marekw1986/EtherGeiger/code/CustomHTTPApp.c

/*********************************************************************
 *
 *  Application to Demo HTTP2 Server
 *  Support for HTTP2 module in Microchip TCP/IP Stack
 *	 -Implements the application 
 *	 -Reference: RFC 1002
 *
 *********************************************************************
 * FileName:        CustomHTTPApp.c
 * Dependencies:    TCP/IP stack
 * Processor:       PIC18, PIC24F, PIC24H, dsPIC30F, dsPIC33F, PIC32
 * Compiler:        Microchip C32 v1.05 or higher
 *					Microchip C30 v3.12 or higher
 *					Microchip C18 v3.30 or higher
 *					HI-TECH PICC-18 PRO 9.63PL2 or higher
 * Company:         Microchip Technology, Inc.
 *
 * Software License Agreement
 *
 * Copyright (C) 2002-2010 Microchip Technology Inc.  All rights
 * reserved.
 *
 * Microchip licenses to you the right to use, modify, copy, and
 * distribute:
 * (i)  the Software when embedded on a Microchip microcontroller or
 *      digital signal controller product ("Device") which is
 *      integrated into Licensee's product; or
 * (ii) ONLY the Software driver source files ENC28J60.c, ENC28J60.h,
 *		ENCX24J600.c and ENCX24J600.h ported to a non-Microchip device
 *		used in conjunction with a Microchip ethernet controller for
 *		the sole purpose of interfacing with the ethernet controller.
 *
 * You should refer to the license agreement accompanying this
 * Software for additional information regarding your rights and
 * obligations.
 *
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
 *
 * Author               Date    Comment
 *~~~~~~~~~~~~~~~~~~~~~~~~~~~~~~~~~~~~~~~~~~~~~~~~~~~~~~~~~~~~~~~~~~~~
 * Elliott Wood     	6/18/07	Original
 ********************************************************************/
#define __CUSTOMHTTPAPP_C

#include <time.h>
#include <string.h>
#include <stdio.h>

#include "TCPIPConfig.h"
#include "config/config.h"
#include "nvram/nvram.h"
#include "time/time.h"
#include "common.h"

#if defined(STACK_USE_HTTP2_SERVER)

#include "net/TCPIP.h"

extern HTTP_CONN curHTTP;
extern HTTP_STUB httpStubs[MAX_HTTP_CONNECTIONS];
extern BYTE curHTTPID;

BYTE token[9];

#if defined (HTTP_USE_POST)
static HTTP_IO_RESULT HTTPPostConfig (void);
static HTTP_IO_RESULT HTTPPostPass (void);
#endif

enum {PASSCHANGE_UNKNOWN, PASSCHANGE_INVALID_TOKEN, PASSCHANGE_EMPTY_OLD, PASSCHANGE_WRONG_OLD, PASSCHANGE_INVALID_NEW, PASSCHANGE_OK};
enum {CFGCHANGE_UNKNOWN, CFGCHANGE_INVALID_TOKEN, CFGCHANGE_INVALID_DHCP, CFGCHANGE_INVALID_IP, CFGCHANGE_INVALID_MAC, CFGCHANGE_INVALID_NETMASK, 
      CFGCHANGE_INVALID_GW, CFGCHANGE_INVALID_DNS1, CFGCHANGE_INVALID_DNS2, CFGCHANGE_INVALID_NTP, CFGCHANGE_INVALID_TIMEZONE, CFGCHANGE_INVALID_DEVNAME, 
      CFGCHANGE_INVALID_MQTT,  CFGCHANGE_INVALID_MQTT_PORT, CFGCHANGE_INVALID_MQTT_USERNAME, CFGCHANGE_INVALID_MQTT_PASSWORD, CFGCHANGE_INVALID_TOPIC, CFGCHANGE_OK};
enum {RESTORE_UNKNOWN, RESTORE_INVALID_TOKEN, RESTORE_OK};

/*****************************************************************************
  Function:
	BYTE HTTPNeedsAuth(BYTE* cFile)
	
  Internal:
  	See documentation in the TCP/IP Stack API or HTTP2.h for details.
  ***************************************************************************/
#if defined(HTTP_USE_AUTHENTICATION)
BYTE HTTPNeedsAuth(BYTE* cFile)
{
    if(memcmppgm2ram(cFile, (ROM void*)"ui/", 3) == 0) return 0x00;
	return 0x80;
}
#endif

/*****************************************************************************
  Function:
	BYTE HTTPCheckAuth(BYTE* cUser, BYTE* cPass)
	
  Internal:
  	See documentation in the TCP/IP Stack API or HTTP2.h for details.
  ***************************************************************************/
#if defined(HTTP_USE_AUTHENTICATION)
BYTE HTTPCheckAuth(BYTE* cUser, BYTE* cPass)
{
    if(strcmppgm2ram((char *)cUser,(ROM char *)"admin") == 0
    && strcmp((char *)cPass, config.password) == 0)
    return 0x80;
	
	return 0x00;
}
#endif

/*********************************************************************
 * Function:        HTTP_IO_RESULT HTTPExecuteGet(void)
 *
 * PreCondition:    curHTTP is loaded
 *
 * Input:           None
 *
 * Output:          HTTP_IO_DONE on success
 *					HTTP_IO_WAITING if waiting for asynchronous process
 *
 * Side Effects:    None
 *
 * Overview:        This function is called if data was read from the
 *					HTTP request from either the GET arguments, or
 *					any cookies sent.  curHTTP.data contains
 *					sequential pairs of strings representing the
 *					data received.  Any required authentication has 
 *					already been validated.
 *
 * Note:            Custom implementation for WebVend Application
 ********************************************************************/
HTTP_IO_RESULT HTTPExecuteGet(void)
{
	BYTE name[20];
    BYTE* ptr;
    
    MPFSGetFilename(curHTTP.file, name, 20);
    if (strcmppgm2ram((char*)name, (ROM char*)"ui/restore.cgi") == 0) {
        ptr = HTTPGetROMArg(curHTTP.data, (ROM BYTE *)"token");
        if ( !ptr || (strcmp((char*)ptr, (char*)token) != 0) ) {
            curHTTP.data[0] = RESTORE_INVALID_TOKEN;
            return HTTP_IO_DONE;
        }
        curHTTP.data[0] = RESTORE_OK;
    }
    else if (strcmppgm2ram((char*)name, (ROM char*)"ui/getarch.cgi") == 0) {
        ptr = HTTPGetROMArg(curHTTP.data, (ROM BYTE *)"mem");
        if (!ptr) { return HTTP_IO_DONE; }
        else if ( strcmppgm2ram((char*)ptr, (ROM char*)"spi") == 0 ) {
            
        }
        else if ( strcmppgm2ram((char*)ptr, (ROM char*)"usb") == 0 ) {
            
        }
        
        ptr = HTTPGetROMArg(curHTTP.data, (ROM BYTE *)"fname");
        
    }
	return HTTP_IO_DONE;
}

#if defined(HTTP_USE_POST)

/*********************************************************************
 * Function:        HTTP_IO_RESULT HTTPExecutePost(void)
 *
 * PreCondition:    curHTTP is loaded
 *
 * Input:           None
 *
 * Output:          HTTP_IO_DONE on success
 *					HTTP_IO_NEED_DATA if more data is requested
 *					HTTP_IO_WAITING if waiting for asynchronous process
 *
 * Side Effects:    None
 *
 * Overview:        This function is called if the request method was
 *					POST.  It is called after HTTPExecuteGet and 
 *					after any required authentication has been validated.
 *
 * Note:            Custom implementation for WebVend Application
 ********************************************************************/
HTTP_IO_RESULT HTTPExecutePost(void) {
	BYTE name[20];
    
    // Load the file name
    MPFSGetFilename(curHTTP.file, name, sizeof(name));
    // Make sure it's the ui/net.htm page
    if (strcmppgm2ram((char*)name, (ROM char*)"ui/config.cgi") == 0) {
		return HTTPPostConfig();
    }
    else if (strcmppgm2ram((char*)name, (ROM char*)"ui/pass.cgi") == 0) {
        return HTTPPostPass();
    }
	return HTTP_IO_DONE;
}

static HTTP_IO_RESULT HTTPPostConfig (void) {
    WORD len;
    config_t newConfig;
    BYTE tokenValid = 0;
    
    curHTTP.data[0] = CFGCHANGE_UNKNOWN;

    // Check to see if the browser is attempting to submit more data than we can parse at once.
	if (curHTTP.byteCount > TCPIsGetReady(sktHTTP) + TCPGetRxFIFOFree(sktHTTP)) return HTTP_IO_DONE;

	// Ensure that all data is waiting to be parsed.  If not, keep waiting for all of it to arrive.
	if (TCPIsGetReady(sktHTTP) < curHTTP.byteCount) return HTTP_IO_NEED_DATA;

    eprom_read((void*)&newConfig, sizeof(newConfig));    
    	
	// Loop while data remains
	while (curHTTP.byteCount) {
		// Check for complete variable
		len = TCPFind(sktHTTP, '&', 0, FALSE);
		if ( (len == 0xFFFF) && (TCPIsGetReady(sktHTTP) == curHTTP.byteCount) ) len = curHTTP.byteCount - 1; //Check if this is the last one

		len = TCPGetArray(sktHTTP, curHTTP.data, len+1);
		curHTTP.byteCount -= len;
		curHTTP.data[len] = '\0';
		HTTPURLDecode(curHTTP.data);
		// Figure out which variable it is
		if (memcmppgm2ram(curHTTP.data, (ROM void*)"token", 5) == 0) {
             if (strcmp(&curHTTP.data[6], token) == 0 ) {
                tokenValid = 1;
            }
            else {
                curHTTP.data[0] = CFGCHANGE_INVALID_TOKEN;
                return HTTP_IO_DONE;
            }
        }
        else if (memcmppgm2ram(curHTTP.data, (ROM void*)"dhcp", 4) == 0) {
			if (memcmppgm2ram(&curHTTP.data[5], (ROM void*)"yes", 3) == 0) {
				newConfig.AppConfig.Flags.bIsDHCPEnabled = TRUE;
			}
			else if (memcmppgm2ram(&curHTTP.data[5], (ROM void*)"no", 2) == 0) {
				newConfig.AppConfig.Flags.bIsDHCPEnabled = FALSE;
			}
            else {
                curHTTP.data[0] = CFGCHANGE_INVALID_DHCP;
                return HTTP_IO_DONE;
            }
		}            
		else if (memcmppgm2ram(curHTTP.data, (ROM void*)"ip", 2) == 0) {
			if (StringToIPAddress(&curHTTP.data[3], &newConfig.AppConfig.MyIPAddr)) {
                newConfig.AppConfig.DefaultIPAddr.Val = newConfig.AppConfig.MyIPAddr.Val;
            }
            else {
                curHTTP.data[0] = CFGCHANGE_INVALID_IP;
                return HTTP_IO_DONE;
            }
		}
        else if (memcmppgm2ram(curHTTP.data, (ROM void*)"mac", 3) == 0) {
            if (StringToMACAddress(&curHTTP.data[4], &newConfig.AppConfig.MyMACAddr)) {
                
            }
            else {
                curHTTP.data[0] = CFGCHANGE_INVALID_MAC;
                return HTTP_IO_DONE;
            }
        }        
		else if (memcmppgm2ram(curHTTP.data, (ROM void*)"netmask", 7) == 0) {
			if (StringToIPAddress(&curHTTP.data[8], &newConfig.AppConfig.MyMask)) {
                newConfig.AppConfig.DefaultMask.Val = newConfig.AppConfig.MyMask.Val;
            }
            else {
                curHTTP.data[0] = CFGCHANGE_INVALID_NETMASK;
                return HTTP_IO_DONE;
            }
		}
		else if (memcmppgm2ram(curHTTP.data, (ROM void*)"gw", 2) == 0) {
			if (!StringToIPAddress(&curHTTP.data[3], &newConfig.AppConfig.MyGateway)) {
                curHTTP.data[0] = CFGCHANGE_INVALID_GW;
                return HTTP_IO_DONE;
            }
		}
		else if (memcmppgm2ram(curHTTP.data, (ROM void*)"dns1", 4) == 0) {
			if (!StringToIPAddress(&curHTTP.data[5], &newConfig.AppConfig.PrimaryDNSServer)) {
                curHTTP.data[0] = CFGCHANGE_INVALID_DNS1;
                return HTTP_IO_DONE;
            }
		}
		else if (memcmppgm2ram(curHTTP.data, (ROM void*)"dns2", 4) == 0) {
			if (!StringToIPAddress(&curHTTP.data[5], &newConfig.AppConfig.SecondaryDNSServer)) {
                curHTTP.data[0] = CFGCHANGE_INVALID_DNS2;
                return HTTP_IO_DONE;
            }
		}
		else if (memcmppgm2ram(curHTTP.data, (ROM void*)"ntp", 3) == 0) {
            if (strlen(&curHTTP.data[4]) && !contain_space(&curHTTP.data[4])) {
                strncpy(newConfig.AppConfig.NtpServer, &curHTTP.data[4], sizeof(newConfig.AppConfig.NtpServer));
            }
            else {
                curHTTP.data[0] = CFGCHANGE_INVALID_NTP;
                return HTTP_IO_DONE;
            }
		}
		else if (memcmppgm2ram(curHTTP.data, (ROM void*)"timezone", 8) == 0) {
            newConfig.timeZone = atoi(&curHTTP.data[9]) * -60;
            if ( (newConfig.timeZone < -780) || (newConfig.timeZone > 660) ) {
                curHTTP.data[0] = CFGCHANGE_INVALID_TIMEZONE;
                return HTTP_IO_DONE;
            }
		}
        else if (memcmppgm2ram(curHTTP.data, (ROM void*)"mqttserver", 10) == 0) {
            if ( (strlen(&curHTTP.data[11]) < sizeof(newConfig.mqtt_server)) && !contain_space(&curHTTP.data[11]) ) {strncpy(newConfig.mqtt_server, &curHTTP.data[11], sizeof(newConfig.mqtt_server)-1);}
            else {
                curHTTP.data[0] = CFGCHANGE_INVALID_MQTT;
                return HTTP_IO_DONE;
            }
        }
        else if (memcmppgm2ram(curHTTP.data, (ROM void*)"mqttusername", 12) == 0) {
            if ( (strlen(&curHTTP.data[13]) < sizeof(newConfig.mqtt_username)) && !contain_space(&curHTTP.data[13]) ) {strncpy(newConfig.mqtt_username, &curHTTP.data[13], sizeof(newConfig.mqtt_username)-1);}
            else {
                curHTTP.data[0] = CFGCHANGE_INVALID_MQTT_USERNAME;
                return HTTP_IO_DONE;
            }
        }
        else if (memcmppgm2ram(curHTTP.data, (ROM void*)"mqttpassword", 12) == 0) {
            if ( (strlen(&curHTTP.data[13]) < sizeof(newConfig.mqtt_password)) && !contain_space(&curHTTP.data[13]) ) {strncpy(newConfig.mqtt_password, &curHTTP.data[13], sizeof(newConfig.mqtt_password)-1);}
            else {
                curHTTP.data[0] = CFGCHANGE_INVALID_MQTT_PASSWORD;
                return HTTP_IO_DONE;
            }
        }         
        else if (memcmppgm2ram(curHTTP.data, (ROM void*)"mqttport", 8) == 0) {
            uint32_t tmpval = strtol(&curHTTP.data[9], NULL, 10);
            if (tmpval) {
                newConfig.mqtt_port = tmpval;
            }
            else {
                curHTTP.data[0] = CFGCHANGE_INVALID_MQTT_PORT;
                return HTTP_IO_DONE;                
            }
        }
        else if (memcmppgm2ram(curHTTP.data, (ROM void*)"topic", 5) == 0) {
            if ( (strlen(&curHTTP.data[6]) < sizeof(newConfig.mqtt_topic)) && !contain_space(&curHTTP.data[6]) ) {strncpy(newConfig.mqtt_topic, &curHTTP.data[6], sizeof(newConfig.mqtt_topic)-1);}
            else {
                curHTTP.data[0] = CFGCHANGE_INVALID_TOPIC;
                return HTTP_IO_DONE;                   
            }
        }
        else if (memcmppgm2ram(curHTTP.data, (ROM void*)"devname", 7) == 0) {
            if ( (strlen(&curHTTP.data[8]) < sizeof(newConfig.devname)) && !contain_space(&curHTTP.data[8])) {
                strncpy(newConfig.devname, &curHTTP.data[8], sizeof(newConfig.devname)-1);
            }
            else {
                curHTTP.data[0] = CFGCHANGE_INVALID_DEVNAME;
                return HTTP_IO_DONE;                      
            }
        }
	}   
    
    if (!tokenValid) {
        curHTTP.data[0] = CFGCHANGE_INVALID_TOKEN;
        return HTTP_IO_DONE;
    }
    
	// Tu zapisujemy zmiany
    eprom_write((void*)&newConfig, sizeof(newConfig));
    curHTTP.data[0] = CFGCHANGE_OK;
	return HTTP_IO_DONE;
}

static HTTP_IO_RESULT HTTPPostPass (void) {
    WORD len;
    config_t newConfig;
    BYTE tokenValid = 0;
    BYTE passValid = 0;
    
    curHTTP.data[0] = PASSCHANGE_UNKNOWN;
    
     // Check to see if the browser is attempting to submit more data than we can parse at once.
	if (curHTTP.byteCount > TCPIsGetReady(sktHTTP) + TCPGetRxFIFOFree(sktHTTP)) return HTTP_IO_DONE;

	// Ensure that all data is waiting to be parsed.  If not, keep waiting for all of it to arrive.
	if (TCPIsGetReady(sktHTTP) < curHTTP.byteCount) return HTTP_IO_NEED_DATA;
    
    eprom_read((void*)&newConfig, sizeof(newConfig));
    
	// Loop while data remains
	while (curHTTP.byteCount) {
		// Check for complete variable
		len = TCPFind(sktHTTP, '&', 0, FALSE);
        if ( (len == 0xFFFF) && (TCPIsGetReady(sktHTTP) == curHTTP.byteCount) ) len = curHTTP.byteCount - 1; //Check if this is the last one

		len = TCPGetArray(sktHTTP, curHTTP.data, len+1);
		curHTTP.byteCount -= len;
		curHTTP.data[len] = '\0';
		HTTPURLDecode(curHTTP.data);
		// Figure out which variable it is
		if (memcmppgm2ram(curHTTP.data, (ROM void*)"token", 5) == 0) {
            if (strcmp(&curHTTP.data[6], token) == 0 ) {
                tokenValid = 1;
            }
            else {
                curHTTP.data[0] = PASSCHANGE_INVALID_TOKEN;                
                return HTTP_IO_DONE;                
            }
		}          
		else if (memcmppgm2ram(curHTTP.data, (ROM void*)"oldpass", 7) == 0) {
			if (strlen(&curHTTP.data[8]) == 0) {
                curHTTP.data[0] = PASSCHANGE_EMPTY_OLD;                
                return HTTP_IO_DONE;
            }
            if (strcmp(&curHTTP.data[8], config.password) == 0 ) {
                passValid = 1;
            }
            else {
                curHTTP.data[0] = PASSCHANGE_WRONG_OLD;                
                return HTTP_IO_DONE;                
            }
		}            
		else if (memcmppgm2ram(curHTTP.data, (ROM void*)"newpass", 7) == 0) {
			if (strlen(&curHTTP.data[8]) == 0) {
                curHTTP.data[0] = PASSCHANGE_INVALID_NEW; 
                return HTTP_IO_DONE;
            }
            strncpy(newConfig.password, &curHTTP.data[8], sizeof(newConfig.password));
		}        
	}
    
    if (!tokenValid || !passValid) return HTTP_IO_DONE;
    
	// Saving new configuration to flash
    eprom_write((void*)&newConfig, sizeof(newConfig));
    curHTTP.data[0] = PASSCHANGE_OK; 
	return HTTP_IO_DONE;
}

#endif //(use_post)

/*********************************************************************
 * Function:        void HTTPPrint_varname(TCP_SOCKET sktHTTP, 
 *							DWORD callbackPos, BYTE *data)
 *
 * PreCondition:    None
 *
 * Input:           sktHTTP: the TCP socket to which to write
 *					callbackPos: 0 initially
 *						return value of last call for subsequent callbacks
 *					data: this connection's data buffer
 *
 * Output:          0 if output is complete
 *					application-defined otherwise
 *
 * Side Effects:    None
 *
 * Overview:        Outputs a variable to the HTTP client.
 *
 * Note:            Return zero to indicate that this callback function 
 *					has finished writing data to the TCP socket.  A 
 *					non-zero return value indicates that more data 
 *					remains to be written, and this callback should 
 *					be called again when more space is available in 
 *					the TCP TX FIFO.  This non-zero return value will 
 *					be the value of the parameter callbackPos for the 
 *					next call.
 ********************************************************************/


void HTTPPrint_dhcpyes(void) {
    if (DHCPIsEnabled(0)) {
        TCPPutROMString(sktHTTP, (ROM void*)" checked");
    }
    return;
}

void HTTPPrint_dhcpno(void) {
    if (!DHCPIsEnabled(0)) {
        TCPPutROMString(sktHTTP, (ROM void*)" checked");
    }    
    return;
}

void HTTPPrint_ipdisp(void) {
    if (DHCPIsEnabled(0)) {
        TCPPutROMString(sktHTTP, (ROM void*)"none");
    }
    else {
        TCPPutROMString(sktHTTP, (ROM void*)"block");
    }
    return;
}

void HTTPPrint_ip(void) {
    int i;
    char buf[4];
    
    for (i=0; i<4; i++) {
        TCPPutString(sktHTTP, itoa(buf, AppConfig.MyIPAddr.v[i], 10));
        if (i < 3) TCPPutROMString(sktHTTP, (ROM void*)".");
    }
    return;
}

void HTTPPrint_mac(void) {
    int i;
    char buf[4];
    
    for (i=0; i<6; i++) {
        snprintf(buf, 3, "%02X", AppConfig.MyMACAddr.v[i]);
        TCPPutString(sktHTTP, buf);
        if (i<5) TCPPutROMString(sktHTTP, (ROM void*)":");
    }
}

void HTTPPrint_netmask(void) {
    int i;
    char buf[4];
    
    for (i=0; i<4; i++) {
        TCPPutString(sktHTTP, itoa(buf, AppConfig.MyMask.v[i], 10));
        if (i < 3) TCPPutROMString(sktHTTP, (ROM void*)".");
    }    
    return;
}

void HTTPPrint_gw(void) {
    int i;
    char buf[4];
    
    for (i=0; i<4; i++) {
        TCPPutString(sktHTTP, itoa(buf, AppConfig.MyGateway.v[i], 10));
        if (i < 3) TCPPutROMString(sktHTTP, (ROM void*)".");
    }    
    return;
}

void HTTPPrint_dns1(void) {
    int i;
    char buf[4];
    
    for (i=0; i<4; i++) {
        TCPPutString(sktHTTP, itoa(buf, AppConfig.PrimaryDNSServer.v[i], 10));
        if (i < 3) TCPPutROMString(sktHTTP, (ROM void*)".");
    }    
    return;
}

void HTTPPrint_dns2(void) {
    int i;
    char buf[4];
    
    for (i=0; i<4; i++) {
        TCPPutString(sktHTTP, itoa(buf, AppConfig.SecondaryDNSServer.v[i], 10));
        if (i < 3) TCPPutROMString(sktHTTP, (ROM void*)".");
    }    
    return;
}

void HTTPPrint_ntp(void) {
    TCPPutString(sktHTTP, AppConfig.NtpServer);
    return;
}

void HTTPPrint_devname(void) {
    TCPPutString(sktHTTP, config.devname);
    return;
}

void HTTPPrint_mqtt_server(void) {
    TCPPutString(sktHTTP, config.mqtt_server);
    return;
}

void HTTPPrint_mqtt_username(void) {
    TCPPutString(sktHTTP, config.mqtt_username);
    return;
}

void HTTPPrint_mqtt_topic(void) {
    TCPPutString(sktHTTP, config.mqtt_topic);
    return;
}

void HTTPPrint_mqtt_port(void) {
    char tmp[32];
    TCPPutString(sktHTTP, itoa(tmp, config.mqtt_port, 10));
    return;
}

void HTTPPrint_newip(void) {
    config_t newConfig;
    int i;
    char buf[4];
    
    eprom_read((void*)&newConfig, sizeof(newConfig));
    
    for (i=0; i<4; i++) {
        TCPPutString(sktHTTP, itoa(buf, newConfig.AppConfig.MyIPAddr.v[i], 10));
        if (i < 3) TCPPutROMString(sktHTTP, (ROM void*)".");
    }
    return;
}

void HTTPPrint_reset(void) {
    Reset();
}

void HTTPPrint_restore(void) {
    switch(curHTTP.data[0]) {
        case RESTORE_INVALID_TOKEN:
        TCPPutROMString(sktHTTP, (ROM void*)"invalid token");
        break;
        
        case RESTORE_OK:
        loadDefaultSettings();
        eprom_write((void*)&config, sizeof(config));
        FormatSpiFlashDisk();
        TCPPutROMString(sktHTTP, (ROM void*)"ok");    
        break;
        
        default:
        TCPPutROMString(sktHTTP, (ROM void*)"unknown_error");
        break;        
    }
}

void HTTPPrint_passChangeStatus (void) {
    switch (curHTTP.data[0]) {
        case PASSCHANGE_INVALID_TOKEN:
        TCPPutROMString(sktHTTP, (ROM void*)"invalid_token");
        break;
                    
        case PASSCHANGE_EMPTY_OLD:
        TCPPutROMString(sktHTTP, (ROM void*)"empty_old");
        break;
        
        case PASSCHANGE_WRONG_OLD:
        TCPPutROMString(sktHTTP, (ROM void*)"wrong_old");  
        break;
        
        case PASSCHANGE_INVALID_NEW:
        TCPPutROMString(sktHTTP, (ROM void*)"invalid_new");
        break;
        
        case PASSCHANGE_OK:
        TCPPutROMString(sktHTTP, (ROM void*)"ok");
        break;
        
        default:
        TCPPutROMString(sktHTTP, (ROM void*)"unknown_error");
        break;
    }
}

void HTTPPrint_configChangeStatus (void) {
    switch (curHTTP.data[0]) {
        case CFGCHANGE_INVALID_TOKEN:
        TCPPutROMString(sktHTTP, (ROM void*)"invalid_token");
        break;
                    
        case CFGCHANGE_INVALID_DHCP:
        TCPPutROMString(sktHTTP, (ROM void*)"invalid_dhcp");
        break;
        
        case CFGCHANGE_INVALID_IP:
        TCPPutROMString(sktHTTP, (ROM void*)"invalid_ip");  
        break;
        
        case CFGCHANGE_INVALID_MAC:
        TCPPutROMString(sktHTTP, (ROM void*)"invalid_mac");  
        break;           
        
        case CFGCHANGE_INVALID_NETMASK:
        TCPPutROMString(sktHTTP, (ROM void*)"invalid_netmask");
        break;
        
        case CFGCHANGE_INVALID_GW:
        TCPPutROMString(sktHTTP, (ROM void*)"invalid_gw");
        break;
        
        case CFGCHANGE_INVALID_DNS1:
        TCPPutROMString(sktHTTP, (ROM void*)"invalid_dns1");
        break;
        
        case CFGCHANGE_INVALID_DNS2:
        TCPPutROMString(sktHTTP, (ROM void*)"invalid_dns2");
        break;
        
        case CFGCHANGE_INVALID_NTP:
        TCPPutROMString(sktHTTP, (ROM void*)"invalid_ntp");
        break;
        
        case CFGCHANGE_INVALID_TIMEZONE:
        TCPPutROMString(sktHTTP, (ROM void*)"invalid_timezone");
        break;
        
        case CFGCHANGE_INVALID_MQTT:
        TCPPutROMString(sktHTTP, (ROM void*)"invalid_mqtt");
        break;
        
        case CFGCHANGE_INVALID_MQTT_PORT:
        TCPPutROMString(sktHTTP, (ROM void*)"invalid_mqttport");
        break;
        
        case CFGCHANGE_INVALID_MQTT_USERNAME:
        TCPPutROMString(sktHTTP, (ROM void*)"invalid_mqttusername");
        break;

        case CFGCHANGE_INVALID_MQTT_PASSWORD:
        TCPPutROMString(sktHTTP, (ROM void*)"invalid_mqttpassword");
        break;        

        case CFGCHANGE_INVALID_TOPIC:
        TCPPutROMString(sktHTTP, (ROM void*)"invalid_topic");
        break;        
        
        case CFGCHANGE_INVALID_DEVNAME:
        TCPPutROMString(sktHTTP, (ROM void*)"invalid_devname");
        break;        
        
        case CFGCHANGE_OK:
        TCPPutROMString(sktHTTP, (ROM void*)"ok");
        break;
        
        default:
        TCPPutROMString(sktHTTP, (ROM void*)"unknown_error");
        break;
    }
}

void HTTPPrint_configToken (void) {
    BYTE i;
    for (i=0; i<8; i++) token[i] = 'a'+(rand() % 26);
    token[8] = '\0';
    TCPPutString(sktHTTP, token);
}

void HTTPPrint_uptime (void) {
    WORD days, hours, minutes;
    DWORD seconds;
    BYTE buff[32];
    
    seconds = uptime();
    
    days = seconds / 86400;
    seconds -= days * 86400;
    hours = seconds / 3600;
    seconds -= hours * 3600;
    minutes = seconds / 60;
    seconds -= minutes * 60;
 
    if (days) {
        sprintf(buff, "%d dni, ", days);
        TCPPutString(sktHTTP, buff);
    }
    sprintf(buff, "%02d:%02d:%02d", hours, minutes, seconds);
    TCPPutString(sktHTTP, buff);
}

void HTTPPrint_uptimesec (void) {
    BYTE buff[16];
    sprintf(buff, "%lu", uptime());
    TCPPutString(sktHTTP, buff);
}

void HTTPPrint_time (void) {
    BYTE buff[64];
    time_t timestamp; 
    
    timestamp = rtccGetTimestamp();
    strncpy(buff, ctime(&timestamp), sizeof(buff)-1);
    TCPPutString(sktHTTP, buff);
}

void HTTPPrint_timestamp (void) {
    BYTE buff[32];

    sprintf(buff, "%lu", rtccGetTimestamp());
    TCPPutString(sktHTTP, buff);
}

void HTTPPrint_timezone (void) {
    BYTE buff[16];
    
    sprintf(buff, "%d", time_zone/-60);
    TCPPutString(sktHTTP, buff);
    
}

void HTTPPrint_cpufreq (void) {
    BYTE buff[16];
    time_t timestamp;
    
    sprintf(buff, "%d", SYSCLK/1000000);
    TCPPutString(sktHTTP, buff);
}

void HTTPPrint_mqttupdate (void) {
    BYTE buff[64];
    if (mqtt_last_publish) {
        snprintf(buff, sizeof(buff)-1, "%d sek. temu", uptime()-mqtt_last_publish);
    }
    else {
        strncpy(buff, "nigdy", sizeof(buff)-1);
    }
    TCPPutString(sktHTTP, buff);
}

void HTTPPrint_mqttstatus (void) {
    TCPPutString(sktHTTP, MQTTConnected() ? "Polaczony" : "Rozlaczony");
}

void HTTPPrint_sensors (void) {
    BYTE buff[512];
    constructJSON((char*)buff, sizeof(buff)-1);
    TCPPutString(sktHTTP, buff);
}

void HTTPPrint_showarch (void) {
    FRESULT res;
    DIR dir;
    static FILINFO fno;
    
    uint16_t i;
    uint8_t first_disk = 1;
    char buff[64];
    
    TCPPutROMString(sktHTTP, (ROM void*)"{\n");
    
    res = f_opendir(&dir, "0:/");
    if (res == FR_OK) {
        if (!first_disk) TCPPutROMString(sktHTTP, (ROM void*)",\n");
        TCPPutROMString(sktHTTP, (ROM void*)"\"spi\" : [\n");
        for (i=0;;i++) {
            res = f_readdir(&dir, &fno);
            if (res != FR_OK || fno.fname[0] == 0) break;
            if (!(fno.fattrib & AM_DIR)) { // It is not a directory
                TCPPutROMString(sktHTTP, (ROM void*)((i > 0) ? ",\n\t{" : "\t{"));
                //json data constructed here
                TCPPutROMString(sktHTTP, (ROM void*)"\"filename\" : \"");
                TCPPutString(sktHTTP, fno.fname);
                TCPPutROMString(sktHTTP, (ROM void*)"\", \"filesize\" : ");
                snprintf(buff, sizeof(buff)-2, "%lu}\n", fno.fsize);
                TCPPutString(sktHTTP, buff);
            }    
        }
        TCPPutROMString(sktHTTP, (ROM void*)"]");
        f_closedir(&dir);
        first_disk = 0;
    }
    
    res = f_opendir(&dir, "1:/");
        if (res == FR_OK) {
        if (!first_disk) TCPPutROMString(sktHTTP, (ROM void*)",\n"); 
        TCPPutROMString(sktHTTP, (ROM void*)"\"usb\" : [\n");
        for (i=0;;i++) {
            res = f_readdir(&dir, &fno);
            if (res != FR_OK || fno.fname[0] == 0) break;
            if (!(fno.fattrib & AM_DIR)) { // It is not a directory
                TCPPutROMString(sktHTTP, (ROM void*)((i > 0) ? ",\n{\t" : "\t{"));
                //json data constructed here
                TCPPutROMString(sktHTTP, (ROM void*)"\"filename\" : \"");
                TCPPutString(sktHTTP, fno.fname);
                TCPPutROMString(sktHTTP, (ROM void*)"\", \"filesize\" : ");
                snprintf(buff, sizeof(buff)-2, "%lu}\n", fno.fsize);
                TCPPutString(sktHTTP, buff);
            }    
        }
        TCPPutROMString(sktHTTP, (ROM void*)"]\n");
        f_closedir(&dir);
        first_disk = 0;
    }
    
    TCPPutROMString(sktHTTP, (ROM void*)"\n}");
}

#endif
