marekw1986/EtherGeiger/code/net/SNTP.c

/*********************************************************************
 *
 *	Simple Network Time Protocol (SNTP) Client Version 3
 *  Module for Microchip TCP/IP Stack
 *	 -Locates an NTP Server from public site using DNS
 *	 -Requests UTC time using SNTP and updates SNTPTime structure
 *	  periodically, according to NTP_QUERY_INTERVAL value
 *	- Reference: RFC 1305
 *
 *********************************************************************
 * FileName:        SNTP.c
 * Dependencies:    UDP, ARP, DNS, Tick
 * Processor:       PIC18, PIC24F, PIC24H, dsPIC30F, dsPIC33F, PIC32
 * Compiler:        Microchip C32 v1.05 or higher
 *					Micrrtochip C30 v3.12 or higher
 *					Microchip C18 v3.30 or higher
 *					HI-TECH PICC-18 PRO 9.63PL2 or higher
 * Company:         Microchip Technology, Inc.
 *
 * Software License Agreement
 *
 * Copyright (C) 2002-2009 Microchip Technology Inc.  All rights
 * reserved.
 *
 * Microchip licenses to you the right to use, modify, copy, and
 * distribute:
 * (i)  the Software when embedded on a Microchip microcontroller or
 *      digital signal controller product ("Device") which is
 *      integrated into Licensee's product; or
 * (ii) ONLY the Software driver source files ENC28J60.c, ENC28J60.h,
 *		ENCX24J600.c and ENCX24J600.h ported to a non-Microchip device
 *		used in conjunction with a Microchip ethernet controller for
 *		the sole purpose of interfacing with the ethernet controller.
 *
 * You should refer to the license agreement accompanying this
 * Software for additional information regarding your rights and
 * obligations.
 *
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
 *
 * Author               Date    	Comment
 *~~~~~~~~~~~~~~~~~~~~~~~~~~~~~~~~~~~~~~~~~~~~~~~~~~~~~~~~~~~~~~~~~~~~
 * Darren Wenn			03/08/07	Original
 * Howard Schlunder		06/20/07	Modified for release
 ********************************************************************/
#define __SNTP_C

#include "../TCPIPConfig.h"

#if defined(STACK_USE_SNTP_CLIENT)

#include "TCPIP.h"

#ifdef SNTP_UPDATE_RTCC
#include <plib.h>
#include <time.h>
extern BYTE rtccSet;
#endif


// Defines how frequently to resynchronize the date/time (default: 10 minutes)
#define NTP_QUERY_INTERVAL		(10ull*60ull * TICK_SECOND)

// Defines how long to wait to retry an update after a failure.
// Updates may take up to 6 seconds to fail, so this 14 second delay is actually only an 8-second retry.
#define NTP_FAST_QUERY_INTERVAL	(14ull * TICK_SECOND)

// Port for contacting NTP servers
#define NTP_SERVER_PORT			(123ul)

// Reference Epoch to use.  (default: 01-Jan-1970 00:00:00)
#define NTP_EPOCH 				(86400ul * (365ul * 70ul + 17ul))

// Defines how long to wait before assuming the query has failed
#define NTP_REPLY_TIMEOUT		(6ul*TICK_SECOND)

// These are normally available network time servers.
// The actual IP returned from the pool will vary every
// minute so as to spread the load around stratum 1 timeservers.
// For best accuracy and network overhead you should locate the 
// pool server closest to your geography, but it will still work
// if you use the global pool.ntp.org address or choose the wrong 
// one or ship your embedded device to another geography.
#ifdef WIFI_NET_TEST
#define NTP_SERVER  "ntp" WIFI_NET_TEST_DOMAIN
#else
#define NTP_SERVER      AppConfig.NtpServer
//#define NTP_SERVER      "ntp1.tp.pl"
//#define NTP_SERVER	"pool.ntp.org"
//#define NTP_SERVER	"europe.pool.ntp.org"
//#define NTP_SERVER	"asia.pool.ntp.org"
//#define NTP_SERVER	"oceania.pool.ntp.org"
//#define NTP_SERVER	"north-america.pool.ntp.org"
//#define NTP_SERVER	"south-america.pool.ntp.org"
//#define NTP_SERVER	"africa.pool.ntp.org"
#endif

// Defines the structure of an NTP packet
typedef struct
{
	struct
	{
		BYTE mode			: 3;	// NTP mode
		BYTE versionNumber 	: 3;	// SNTP version number
		BYTE leapIndicator	: 2;	// Leap second indicator
	} flags;						// Flags for the packet

	BYTE stratum;					// Stratum level of local clock
	CHAR poll;						// Poll interval
	CHAR precision;					// Precision (seconds to nearest power of 2)
	DWORD root_delay;				// Root delay between local machine and server
	DWORD root_dispersion;			// Root dispersion (maximum error)
	DWORD ref_identifier;			// Reference clock identifier
	DWORD ref_ts_secs;				// Reference timestamp (in seconds)
	DWORD ref_ts_fraq;				// Reference timestamp (fractions)
	DWORD orig_ts_secs;				// Origination timestamp (in seconds)
	DWORD orig_ts_fraq;				// Origination timestamp (fractions)
	DWORD recv_ts_secs;				// Time at which request arrived at sender (seconds)
	DWORD recv_ts_fraq;				// Time at which request arrived at sender (fractions)
	DWORD tx_ts_secs;				// Time at which request left sender (seconds)
	DWORD tx_ts_fraq;				// Time at which request left sender (fractions)
} NTP_PACKET;

// Seconds value obtained by last update
static DWORD dwSNTPSeconds = 0;

// Tick count of last update
static DWORD dwLastUpdateTick = 0;

/*****************************************************************************
  Function:
	void SNTPClient(void)

  Summary:
	Periodically checks the current time from a pool of servers.

  Description:
	This function periodically checks a pool of time servers to obtain the
	current date/time.

  Precondition:
	UDP is initialized.

  Parameters:
	None

  Returns:
  	None
  	
  Remarks:
	This function requires once available UDP socket while processing, but
	frees that socket when the SNTP module is idle.
  ***************************************************************************/
void SNTPClient(void)
{
	NTP_PACKET			pkt;
	WORD		 		w;
//	static NODE_INFO	Server;
	static DWORD		dwTimer;
	static UDP_SOCKET	MySocket = INVALID_UDP_SOCKET;
	static enum
	{
		SM_HOME = 0,
		SM_UDP_IS_OPENED,
		//SM_NAME_RESOLVE,
		//SM_ARP_START_RESOLVE,
		//SM_ARP_RESOLVE,
		//SM_ARP_START_RESOLVE2,
		//SM_ARP_RESOLVE2,
		//SM_ARP_START_RESOLVE3,
		//SM_ARP_RESOLVE3,
		//SM_ARP_RESOLVE_FAIL,
		SM_UDP_SEND,
		SM_UDP_RECV,
		SM_SHORT_WAIT,
		SM_WAIT
	} SNTPState = SM_HOME;


	switch(SNTPState)
	{
		case SM_HOME:
			if(MySocket == INVALID_UDP_SOCKET)
				MySocket = UDPOpenEx((DWORD)(PTR_BASE)NTP_SERVER,UDP_OPEN_ROM_HOST,0,NTP_SERVER_PORT);
			dwTimer = TickGetDiv64K();
			SNTPState++;
			break;
			
		case SM_UDP_IS_OPENED:
			if(UDPIsOpened(MySocket) == TRUE)
			{
				//printf("SNTP: opened\r\n");
                SNTPState = SM_UDP_SEND;
			}
            //tmout waitng for sOpened
            if(TickGetDiv64K() - dwTimer > (NTP_FAST_QUERY_INTERVAL/65536ull))
            {
                UDPClose(MySocket);
                SNTPState = SM_HOME;
                MySocket = INVALID_UDP_SOCKET;
            }
			break;

#if 0			
			// Obtain ownership of the DNS resolution module
			if(!DNSBeginUsage())
				break;

			// Obtain the IP address associated with the server name
			DNSResolveROM((ROM BYTE*)NTP_SERVER, DNS_TYPE_A);
			dwTimer = TickGet();
			SNTPState = SM_NAME_RESOLVE;
			break;

		case SM_NAME_RESOLVE:
			// Wait for DNS resolution to complete
			if(!DNSIsResolved(&Server.IPAddr)) 
			{
				if((TickGet() - dwTimer) > (5 * TICK_SECOND)) 
				{
					DNSEndUsage();
					dwTimer = TickGetDiv64K();
					SNTPState = SM_SHORT_WAIT;
				}
				break;
			}
			
			// Obtain DNS resolution result
			if(!DNSEndUsage())
			{
				// No valid IP address was returned from the DNS 
				// server.  Quit and fail for a while if host is not valid.
				dwTimer = TickGetDiv64K();
				SNTPState = SM_SHORT_WAIT;
				break;
			}
			SNTPState = SM_ARP_START_RESOLVE;
			// No need to break

		case SM_ARP_START_RESOLVE:
		case SM_ARP_START_RESOLVE2:
		case SM_ARP_START_RESOLVE3:
			// Obtain the MAC address associated with the server's IP address 
			ARPResolve(&Server.IPAddr);
			dwTimer = TickGet();
			SNTPState++;
			break;

		case SM_ARP_RESOLVE:
		case SM_ARP_RESOLVE2:
		case SM_ARP_RESOLVE3:
			// Wait for the MAC address to finish being obtained
			if(!ARPIsResolved(&Server.IPAddr, &Server.MACAddr))
			{
				// Time out if too much time is spent in this state
				if(TickGet() - dwTimer > 1*TICK_SECOND)
				{
					// Retransmit ARP request by going to next SM_ARP_START_RESOLVE state or fail by going to SM_ARP_RESOLVE_FAIL state.
					SNTPState++;
				}
				break;
			}
			SNTPState = SM_UDP_SEND;
			break;

		case SM_ARP_RESOLVE_FAIL:
			// ARP failed after 3 tries, abort and wait for next time query
			dwTimer = TickGetDiv64K();
			SNTPState = SM_SHORT_WAIT;
			break;
#endif
// case SM_UDP_IS_OPENED:
		case SM_UDP_SEND:
			// Open up the sending UDP socket
			//MySocket = UDPOpen(0, &Server, NTP_SERVER_PORT);
#if 0

			MySocket = UDPOpenEx(NTP_SERVER,UDP_OPEN_ROM_HOST,0,NTP_SERVER_PORT);
			if(MySocket == INVALID_UDP_SOCKET)
				break;
#endif			

			// Make certain the socket can be written to
			if(!UDPIsPutReady(MySocket))
			{
				UDPClose(MySocket);
				SNTPState = SM_HOME;
				MySocket = INVALID_UDP_SOCKET;
				break;
			}

			// Transmit a time request packet
			memset(&pkt, 0, sizeof(pkt));
			pkt.flags.versionNumber = 3;	// NTP Version 3
			pkt.flags.mode = 3;				// NTP Client
			pkt.orig_ts_secs = swapl(NTP_EPOCH);
			UDPPutArray((BYTE*) &pkt, sizeof(pkt));	
			UDPFlush();	
			
			dwTimer = TickGet();
			SNTPState = SM_UDP_RECV;		
			break;

		case SM_UDP_RECV:
			// Look for a response time packet
			if(!UDPIsGetReady(MySocket)) 
			{
				if((TickGet()) - dwTimer > NTP_REPLY_TIMEOUT)
				{
					// Abort the request and wait until the next timeout period
					UDPClose(MySocket);
					//dwTimer = TickGetDiv64K();
					//SNTPState = SM_SHORT_WAIT;
					SNTPState = SM_HOME;
					MySocket = INVALID_UDP_SOCKET;
					break;
				}
				break;
			}
			
			// Get the response time packet
			w = UDPGetArray((BYTE*) &pkt, sizeof(pkt));
			UDPClose(MySocket);
			dwTimer = TickGetDiv64K();
			SNTPState = SM_WAIT;
			MySocket = INVALID_UDP_SOCKET;
			
			// Validate packet size
			if(w != sizeof(pkt)) 
			{
				break;	
			}
			
			// Set out local time to match the returned time
			dwLastUpdateTick = TickGet();
			dwSNTPSeconds = swapl(pkt.tx_ts_secs) - NTP_EPOCH;
			// Do rounding.  If the partial seconds is > 0.5 then add 1 to the seconds count.
			if(((BYTE*)&pkt.tx_ts_fraq)[0] & 0x80)
				dwSNTPSeconds++;

			#ifdef WIFI_NET_TEST
				wifi_net_test_print("SNTP: current time", dwSNTPSeconds);
			#endif

            #ifdef SNTP_UPDATE_RTCC
                struct tm *current_time = gmtime(&dwSNTPSeconds);
                rtccTime time;
                rtccDate date;
                
                time.l = 0;
                date.l = 0;
                time.hour = ByteToBcd(current_time->tm_hour);
                time.min = ByteToBcd(current_time->tm_min);
                time.sec = ByteToBcd(current_time->tm_sec);
                date.mday = ByteToBcd(current_time->tm_mday);
                date.mon = ByteToBcd(current_time->tm_mon);
                date.year = ByteToBcd(current_time->tm_year);
                RtccSetTimeDate(time.l, date.l);
                rtccSet = 1;
            #endif
			break;

		case SM_SHORT_WAIT:
			// Attempt to requery the NTP server after a specified NTP_FAST_QUERY_INTERVAL time (ex: 8 seconds) has elapsed.
			if(TickGetDiv64K() - dwTimer > (NTP_FAST_QUERY_INTERVAL/65536ull))
			{
				SNTPState = SM_HOME;
				MySocket = INVALID_UDP_SOCKET;
			}
			break;

		case SM_WAIT:
			// Requery the NTP server after a specified NTP_QUERY_INTERVAL time (ex: 10 minutes) has elapsed.
			if(TickGetDiv64K() - dwTimer > (NTP_QUERY_INTERVAL/65536ull))
			{
				SNTPState = SM_HOME;
				MySocket = INVALID_UDP_SOCKET;
			}

			break;
	}
}


/*****************************************************************************
  Function:
	DWORD SNTPGetUTCSeconds(void)

  Summary:
	Obtains the current time from the SNTP module.

  Description:
	This function obtains the current time as reported by the SNTP module.  
	Use this value for absolute time stamping.  The value returned is (by
	default) the number of seconds since 01-Jan-1970 00:00:00.

  Precondition:
	None

  Parameters:
	None

  Returns:
  	The number of seconds since the Epoch.  (Default 01-Jan-1970 00:00:00)
  	
  Remarks:
	Do not use this function for time difference measurements.  The Tick
	module is more appropriate for those requirements.
  ***************************************************************************/
DWORD SNTPGetUTCSeconds(void)
{
	DWORD dwTickDelta;
	DWORD dwTick;

	// Update the dwSNTPSeconds variable with the number of seconds 
	// that has elapsed
	dwTick = TickGet();
	dwTickDelta = dwTick - dwLastUpdateTick;
	while(dwTickDelta > TICK_SECOND)
	{
		dwSNTPSeconds++;
		dwTickDelta -= TICK_SECOND;
	}
	
	// Save the tick and residual fractional seconds for the next call
	dwLastUpdateTick = dwTick - dwTickDelta;

	return dwSNTPSeconds;
}

#endif  //if defined(STACK_USE_SNTP_CLIENT)
